sebseb7/pentawall/masterModule/usart.h

#ifndef _USART_H
#define _USART_H


// Baud rate of the USART
#define USART_BAUD 500000	


void USART_Init (void);
void USART_putc (char c);
uint8_t uart_getc_nb(uint8_t*);


//*****************************************************************************
//Anpassen der seriellen Schnittstellen Register
#define USART_RXC_vect USART0_RX_vect
//-----------------------
#define UCSRA		UCSR0A
#define UCSRB		UCSR0B
#define UCSRC		UCSR0C
#define UDR			UDR0
#define UBRRL		UBRR0L
#define UBRRH		UBRR0H

// UCSRA
#define	RXC			RXC0
#define TXC			TXC0
#define UDRE		UDRE0
#define FE			FE0
#define UPE			UPE0
#define U2X			U2X0
#define MPCM		MPCM0

// UCSRB
#define RXCIE		RXCIE0
#define TXCIE		TXCIE0
#define UDRIE		UDRIE0
#define TXEN		TXEN0
#define RXEN		RXEN0
#define UCSZ2		UCSZ02
#define RXB8		RXB80
#define TXB8		TXB80

// UCSRC
#define UMSEL1	UMSEL01
#define UMSEL0	UMSEL00
#define UPM1		UPM01
#define UPM0		UPM00
#define USBS		USBS0
#define UCSZ1		UCSZ01
#define UCSZ0		UCSZ00
#define UCPOL		UCPOL0
//-----------------------


#endif
